holmesrichards/MFOS-SVF/Images/IMG_20200320_130129.jpg

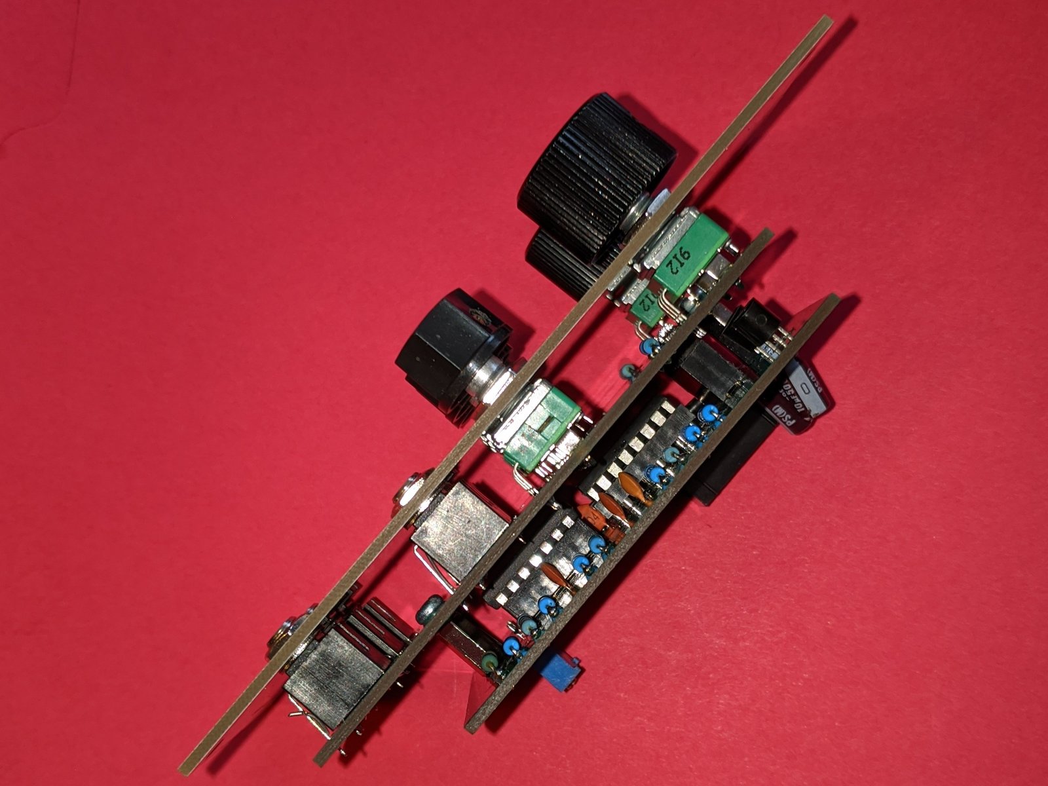
Images/IMG_20200320_130129.jpg
