holmesrichards/MFOS-SVF/Images/IMG_20200320_130210.jpg

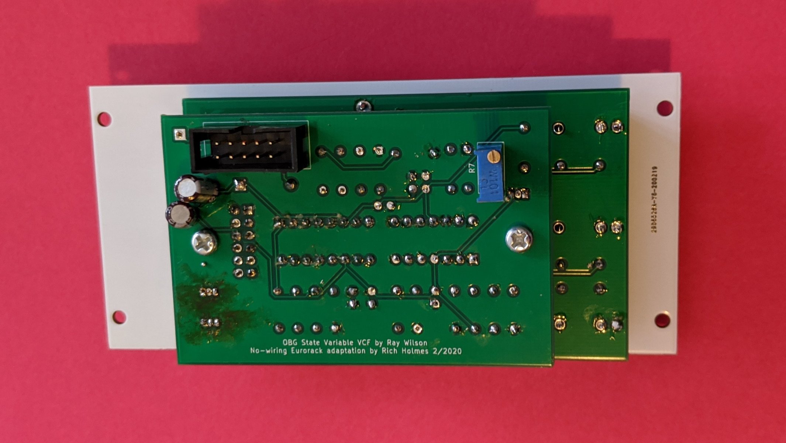
Images/IMG_20200320_130210.jpg
